Claudiobrau/SIMAA-I-Sistema-Inteligente-de-Monitoramento-Ambiental-e-Ac-stico-./Imagens/WhatsApp Image 2026-04-21 at 15.52.27.jpeg

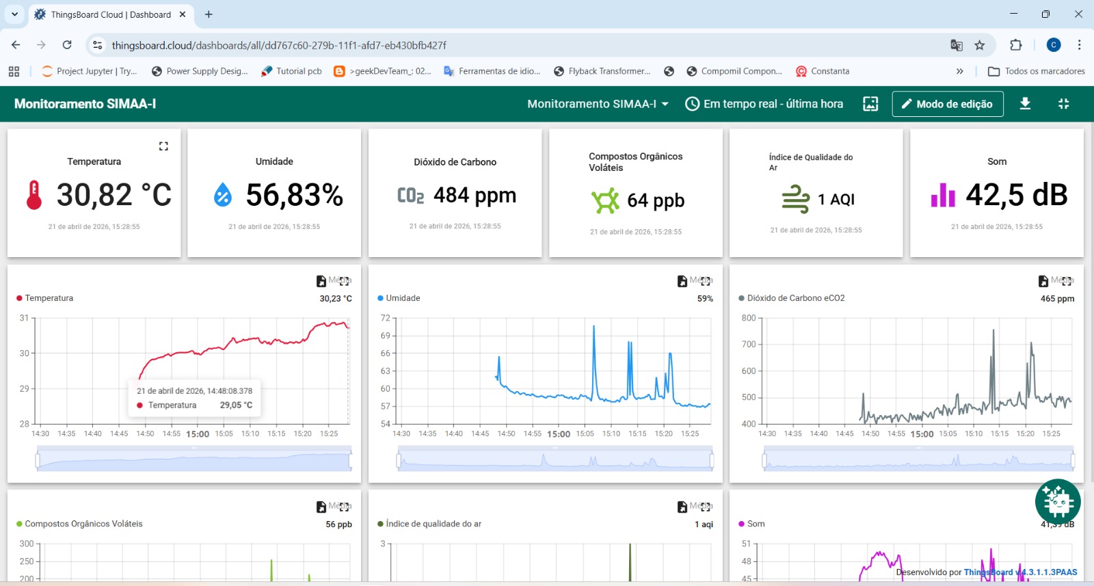
Imagens/WhatsApp Image 2026-04-21 at 15.52.27.jpeg
