Claudiobrau/SIMAA-I-Sistema-Inteligente-de-Monitoramento-Ambiental-e-Ac-stico-./Imagens/WhatsApp Image 2026-05-10 at 19.59.46 (3).jpeg

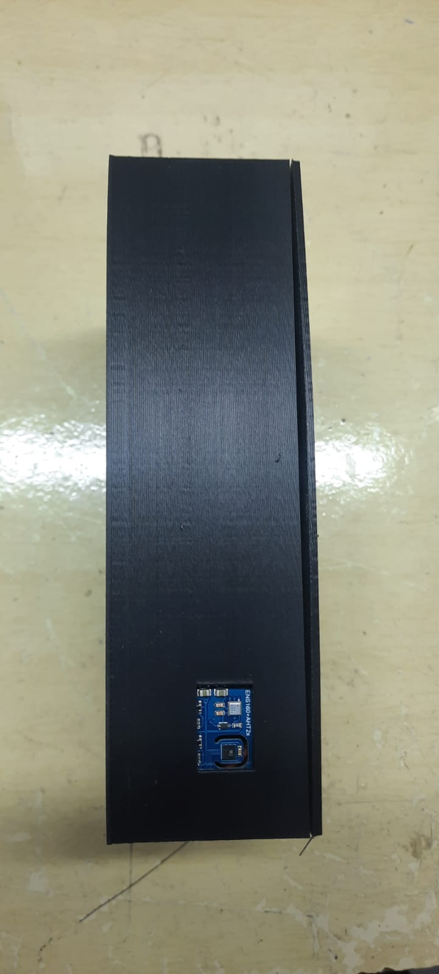
Imagens/WhatsApp Image 2026-05-10 at 19.59.46 (3).jpeg
