Claudiobrau/SIMAA-I-Sistema-Inteligente-de-Monitoramento-Ambiental-e-Ac-stico-./Imagens/WhatsApp Image 2026-05-19 at 12.08.54 (1).jpeg

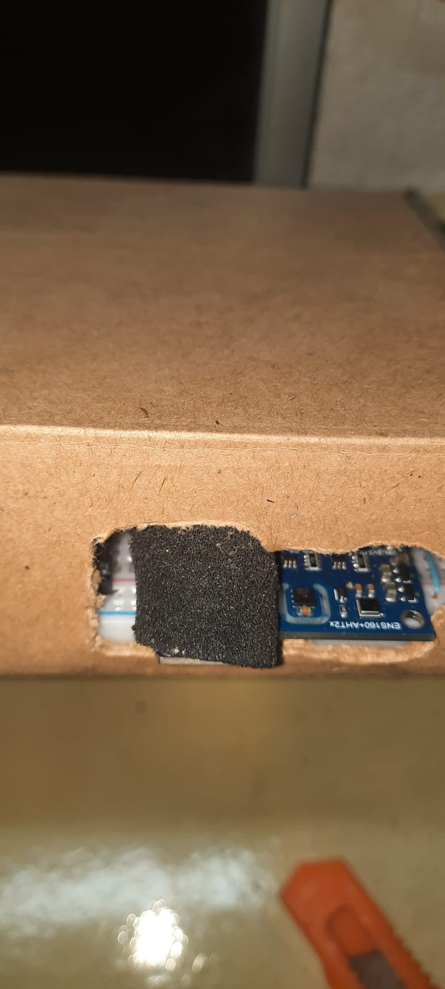
Imagens/WhatsApp Image 2026-05-19 at 12.08.54 (1).jpeg
